gavin4d/dangerDonut/components/arduino/docs/source/_static/external_library_test_pr.png

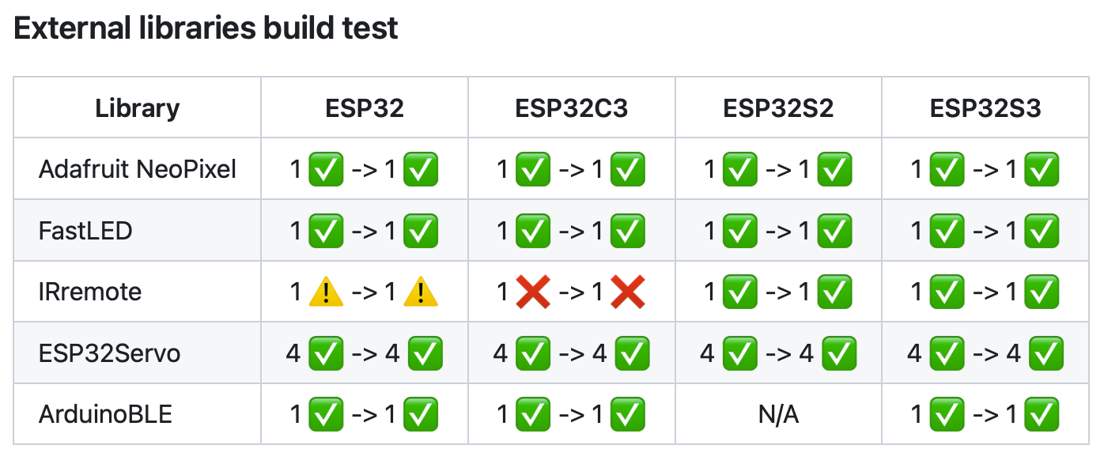
components/arduino/docs/source/_static/external_library_test_pr.png
