gavin4d/dangerDonut/components/arduino/docs/source/_static/external_library_test_schedule.png

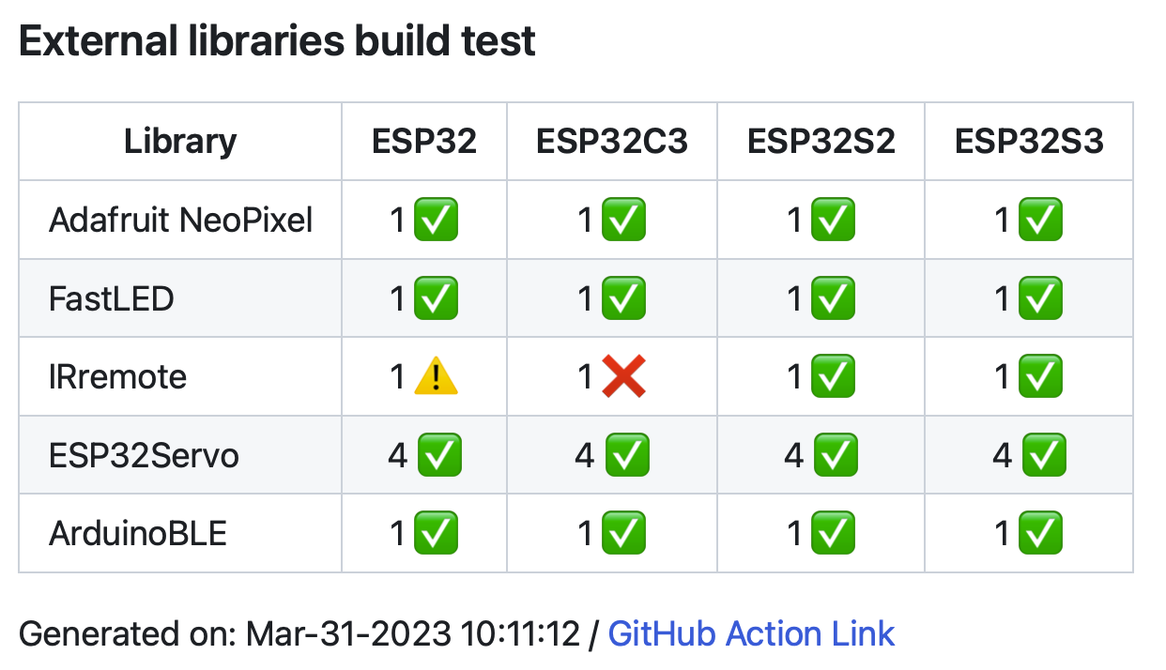
components/arduino/docs/source/_static/external_library_test_schedule.png
