gavin4d/dangerDonut/components/POVDisplay/imageData.h

#ifndef IMAGEDATA_H
#define IMAGEDATA_H
#include <stdint.h>

#define NUM_SPRITES 27

const unsigned int digit_0 [] = {
0xffffffff, 0xffffffff, 0xffffffff, 0xffffffff, 0xffffffff, 0xffffffff, 0xffffffff, 0xffffffff, 0xffffffff, 0xffffffff, 0xffffffff, 0xffffffff, 0x00000000, 0xffffffff, 0xffffffff, 0xffffffff, 0xffffffff, 0x00000000, 0xffffffff, 0xffffffff, 0xffffffff, 0xffffffff, 0x00ffffff, 0xffffffff, 0xffffffff, 0xffffffff, 0xffffffff, 0x00ffffff, 0xffffffff, 0xffffffff, 0xffffffff, 0xffffffff, 0x00000000, 0xffffffff, 0xffffffff, 0xffffffff, 0xffffffff, 0x00000000, 0xffffffff, 0xffffffff, 0xffffffff, 0xffffffff, 0xffffffff, 0xffffffff, 0xffffffff, 0xffffffff, 0xffffffff, 0xffffffff, 0xffffffff, 0xffffffff
};

const unsigned int digit_1 [] = {
0xffffffff, 0xffffffff, 0xffffffff, 0xffffffff, 0xffffffff, 0xffffffff, 0x00000000, 0xffffffff, 0xffffffff, 0x00000000, 0xffffffff, 0xffffffff, 0x00000000, 0xffffffff, 0xffffffff, 0x00000000, 0xffffffff, 0xffffffff, 0x00000000, 0xffffffff, 0xffffffff, 0x00000000, 0xffffffff, 0xffffffff, 0x00000000, 0xffffffff, 0xffffffff, 0x00000000, 0xffffffff, 0xffffffff
};

const unsigned int digit_2 [] = {
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
    {5,10},
    {5,10},
    {5,10},
    {5,10},
    {5,10},
    {5,10},
    {5,10},
    {18,8},
    {84,10},
    {38,10},
    {38,10},
    {7,7},
    {7,7},
    {7,7},
    {7,7},
    {1,10},
    {1,10},
    {1,10},
    {1,10},
    {1,10},
    {1,10},
    {1,10},
    {1,10},
    {1,10}
};
#endif
